MOSH-Insa-Toulouse/2025-2026-4GP-barre-bacchin/KiCad/Modele-3D-Kicad/female-header-pins-2-54-mm-pitch-1.snapshot.3/Header Pins/Renders/header.JPG

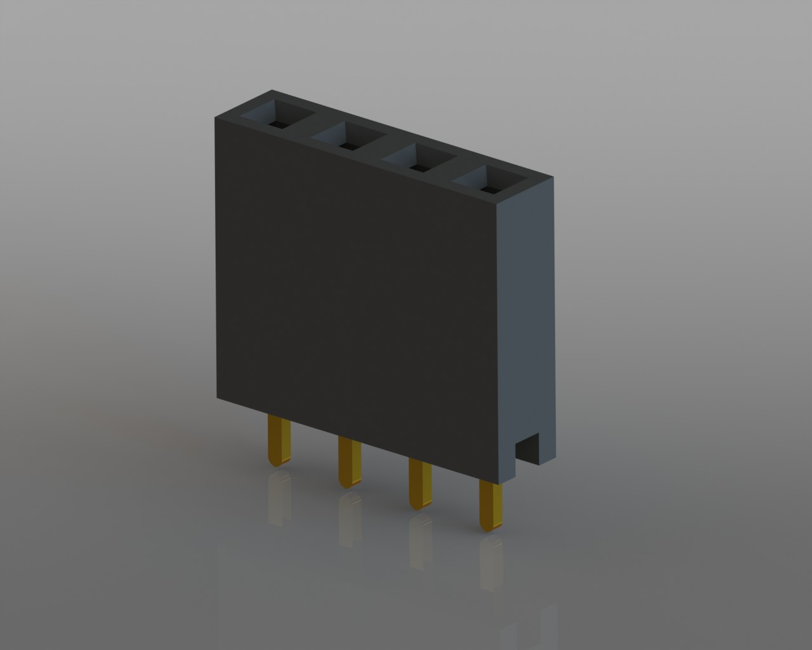
KiCad/Modele-3D-Kicad/female-header-pins-2-54-mm-pitch-1.snapshot.3/Header Pins/Renders/header.JPG
