MOSH-Insa-Toulouse/2025-2026-4GP-barre-bacchin/KiCad/Modele-3D-Kicad/hc-05-bluetooth-module-3.snapshot.1/hc-05_2019-Dec-28_09-18-33PM-000_CustomizedView16164692095.png

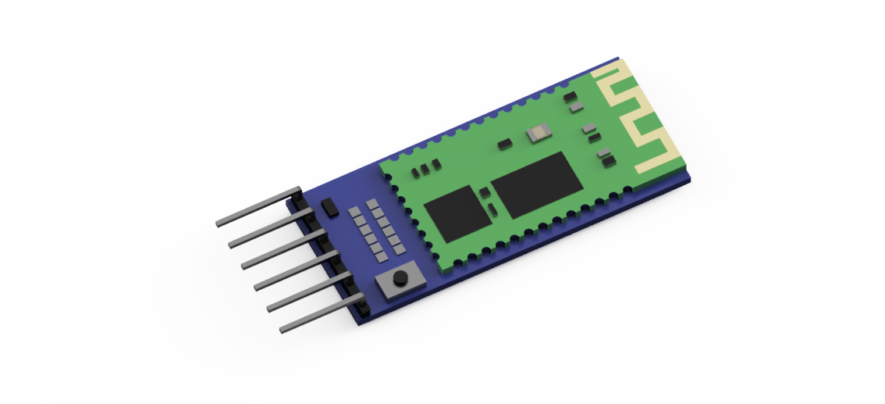
KiCad/Modele-3D-Kicad/hc-05-bluetooth-module-3.snapshot.1/hc-05_2019-Dec-28_09-18-33PM-000_CustomizedView16164692095.png
