MOSH-Insa-Toulouse/2025-2026-4GP-barre-bacchin/KiCad/Modele-3D-Kicad/pin-header-female-2-54mm-different-pin-numbers-1.snapshot.4/Pin_Header-Female-2.54mm_V3.png

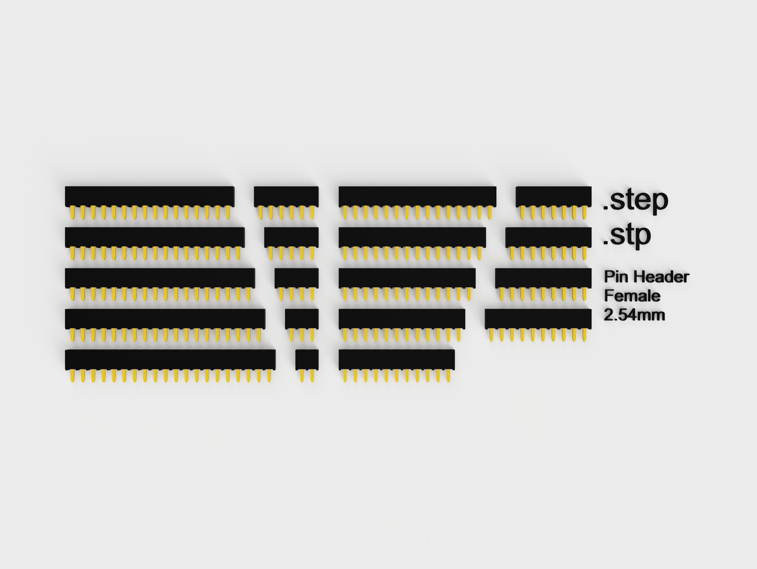
KiCad/Modele-3D-Kicad/pin-header-female-2-54mm-different-pin-numbers-1.snapshot.4/Pin_Header-Female-2.54mm_V3.png
