MOSH-Insa-Toulouse/2025-2026-4GP-barre-bacchin/KiCad/Modele-3D-Kicad/pin-header-female-2-54mm-different-pin-numbers-1.snapshot.4/16-Pin Header - Female - 2.54mm.step

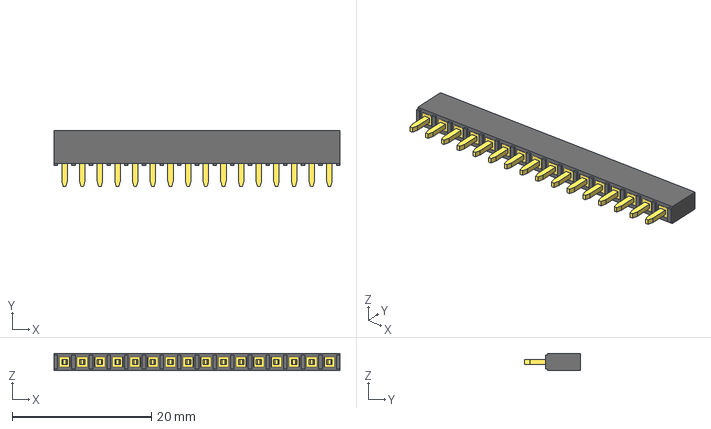
[picture p38: CAD file, 2026-04-16]
KiCad/Modele-3D-Kicad/pin-header-female-2-54mm-different-pin-numbers-1.snapshot.4/16-Pin Header - Female - 2.54mm.step
41.1 x 8.00 x 2.50 mm
