MOSH-Insa-Toulouse/2025-2026-4GP-barre-bacchin/KiCad/Modele-3D-Kicad/pin-header-female-2-54mm-different-pin-numbers-1.snapshot.4/18-Pin Header - Female - 2.54mm.step

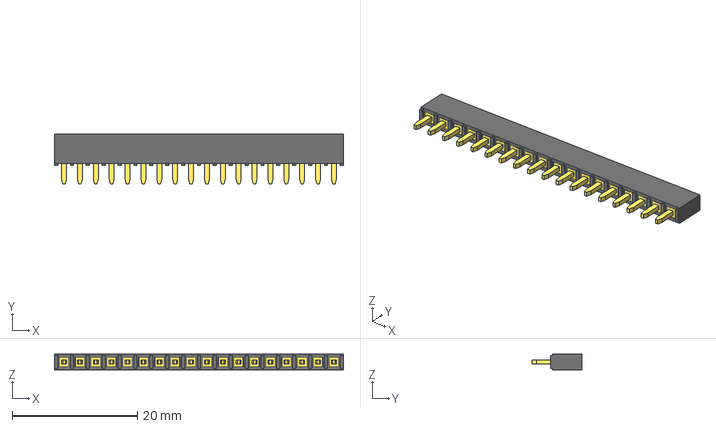
[picture p40: CAD file, 2026-04-16]
KiCad/Modele-3D-Kicad/pin-header-female-2-54mm-different-pin-numbers-1.snapshot.4/18-Pin Header - Female - 2.54mm.step
46.2 x 8.00 x 2.50 mm
