MOSH-Insa-Toulouse/2025-2026-4GP-barre-bacchin/KiCad/Modele-3D-Kicad/pin-header-female-2-54mm-different-pin-numbers-1.snapshot.4/2-Pin Header - Female - 2.54mm.step

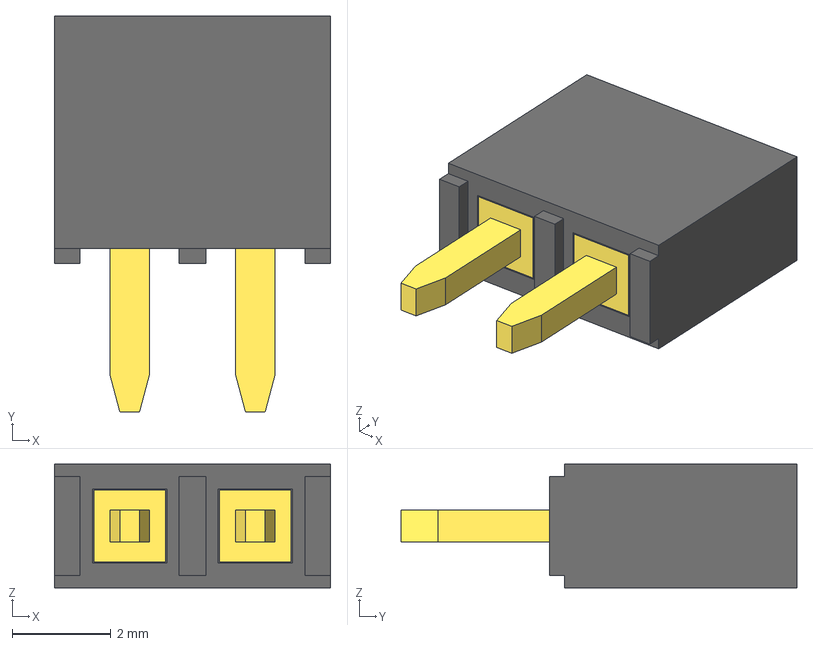
[picture p42: CAD file, 2026-04-16]
KiCad/Modele-3D-Kicad/pin-header-female-2-54mm-different-pin-numbers-1.snapshot.4/2-Pin Header - Female - 2.54mm.step
5.58 x 8.00 x 2.50 mm
