MOSH-Insa-Toulouse/2025-2026-4GP-barre-bacchin/LTSpice/amplifier_final_draft.asc

C1: cap; 100n
C2: cap; {C2}
C3: cap; 100n
C4: cap; 1p
R1: res; 100k
R2: res; 1k
R3: res; 10k
R4: res; 100k
R5: res; 1k
U1: LTC1050
V1: voltage; SINE(0 325 50)
V2: voltage; 5
V3: voltage; PULSE(0 1 0.2 0.1 0.1 1); AC 1
X1: Symbaule
Named nets: 0, ADC
.tran 2
;ac dec 1000 0.1 1000k
.param G0 10n
.param G1 10n
.param R1 100k
.step param C2 100n 2u 100n
